iesgrancapitan-proyectos/202021asir_junio_ControlCalidadAire-escurtu696/Guiatecnica/1.PNG

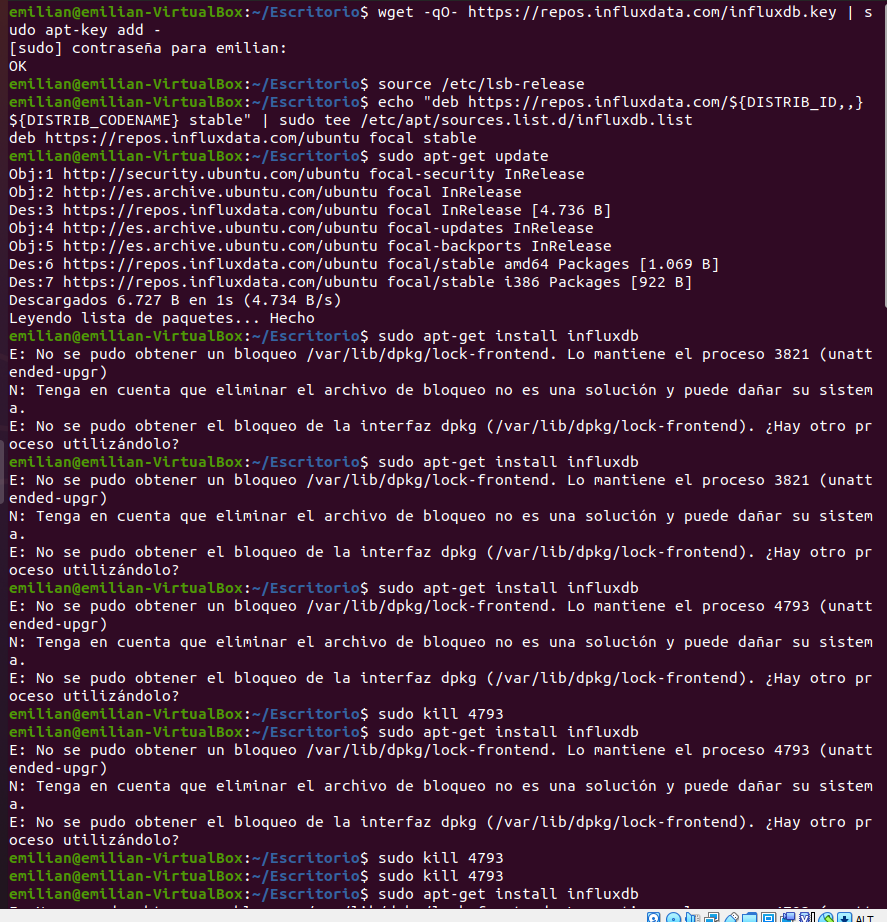
Guiatecnica/1.PNG
