iesgrancapitan-proyectos/202021asir_junio_ControlCalidadAire-escurtu696/Guiatecnica/2.PNG

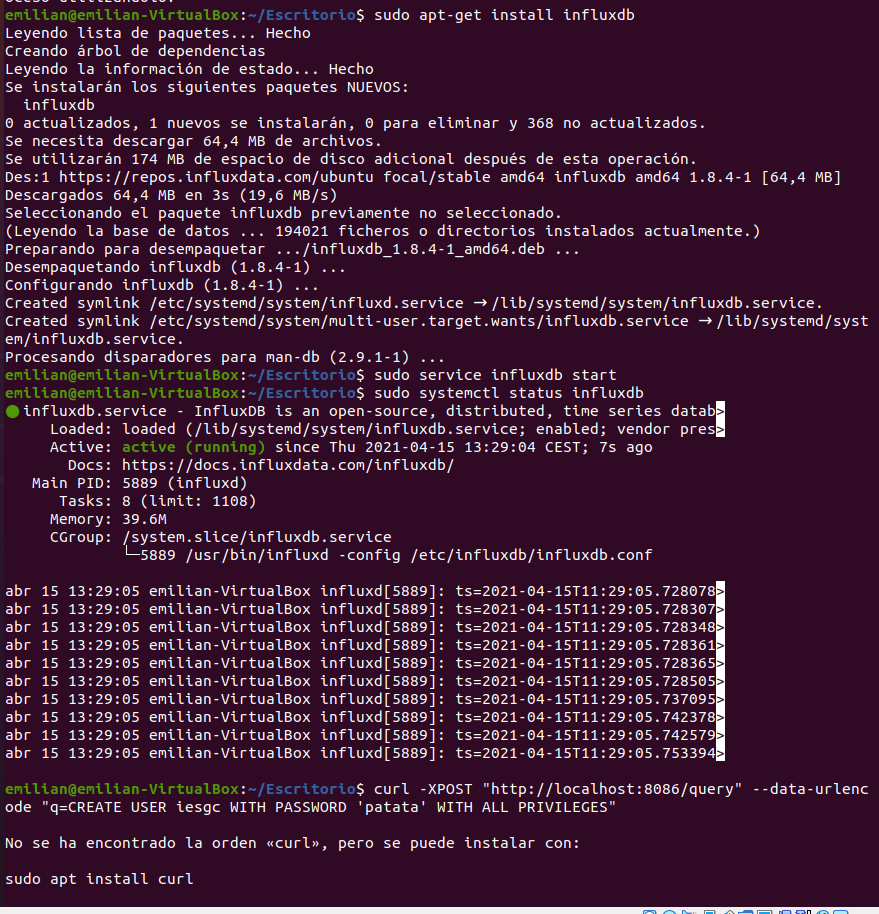
Guiatecnica/2.PNG
