iesgrancapitan-proyectos/202021asir_junio_ControlCalidadAire-escurtu696/Guiatecnica/3.PNG

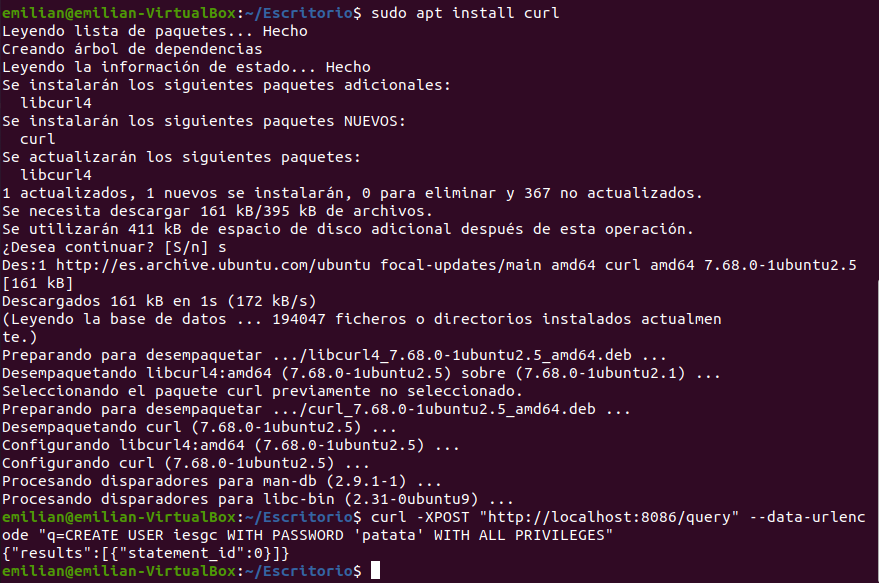
Guiatecnica/3.PNG
