iesgrancapitan-proyectos/202021asir_junio_ControlCalidadAire-escurtu696/Guiatecnica/4.PNG

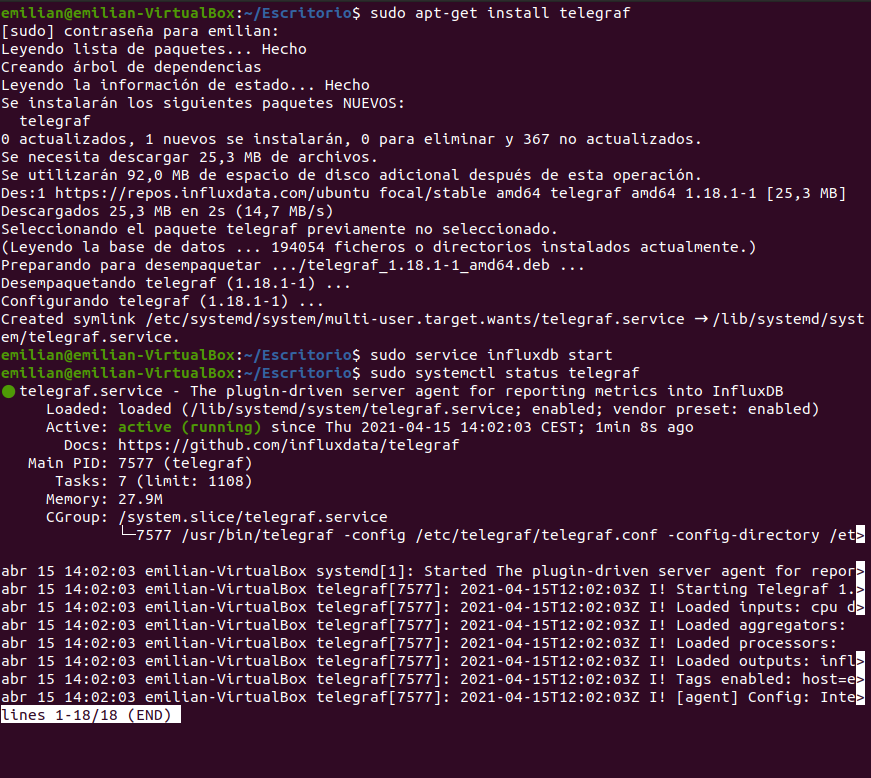
Guiatecnica/4.PNG
