iesgrancapitan-proyectos/202021asir_junio_ControlCalidadAire-escurtu696/Guiatecnica/5.PNG

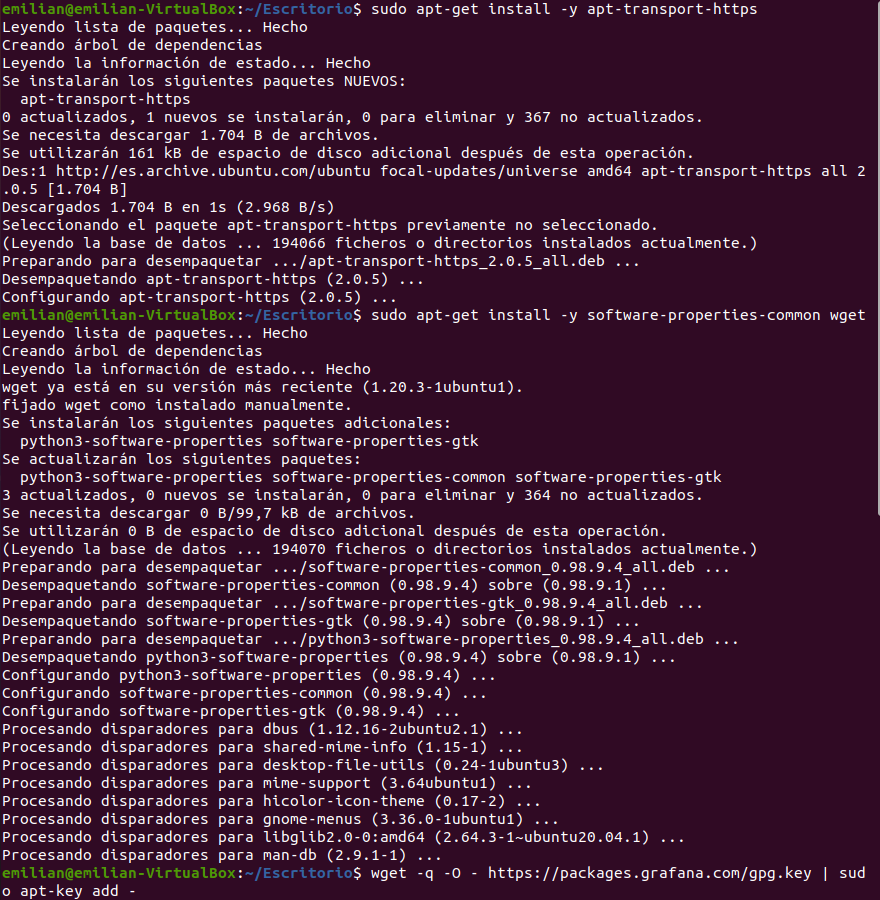
Guiatecnica/5.PNG
