iesgrancapitan-proyectos/202021asir_junio_ControlCalidadAire-escurtu696/Guiatecnica/6.PNG

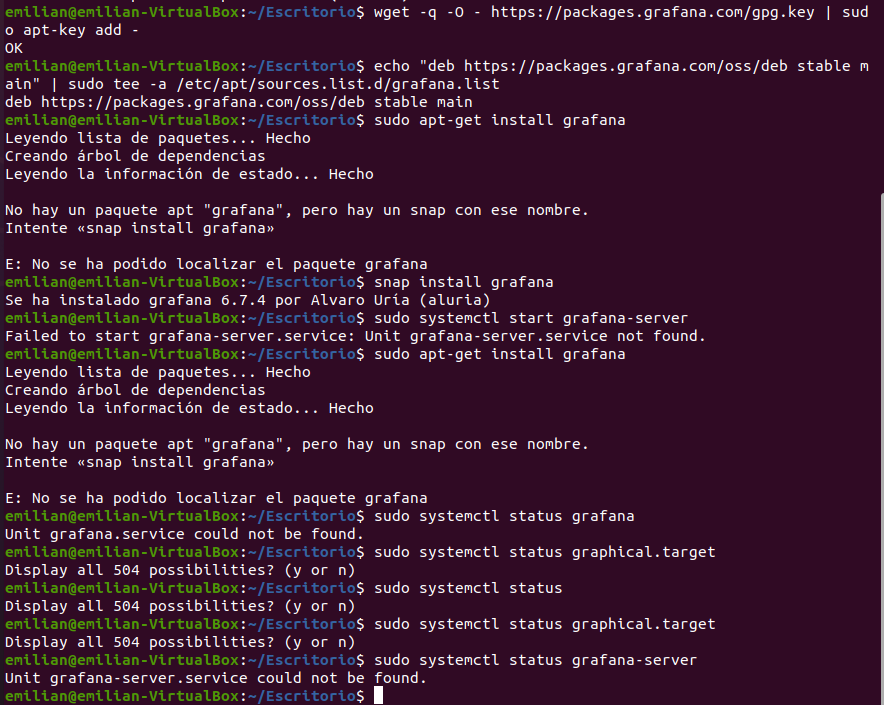
Guiatecnica/6.PNG
