iesgrancapitan-proyectos/202021asir_junio_ControlCalidadAire-escurtu696/Guiatecnica/7.PNG

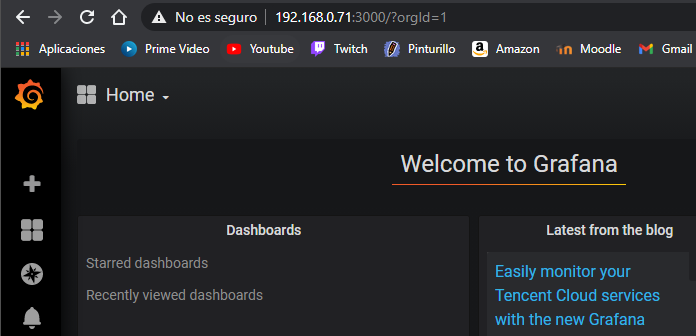
Guiatecnica/7.PNG
