iesgrancapitan-proyectos/202021asir_junio_ControlCalidadAire-escurtu696/Guiatecnica/8.PNG

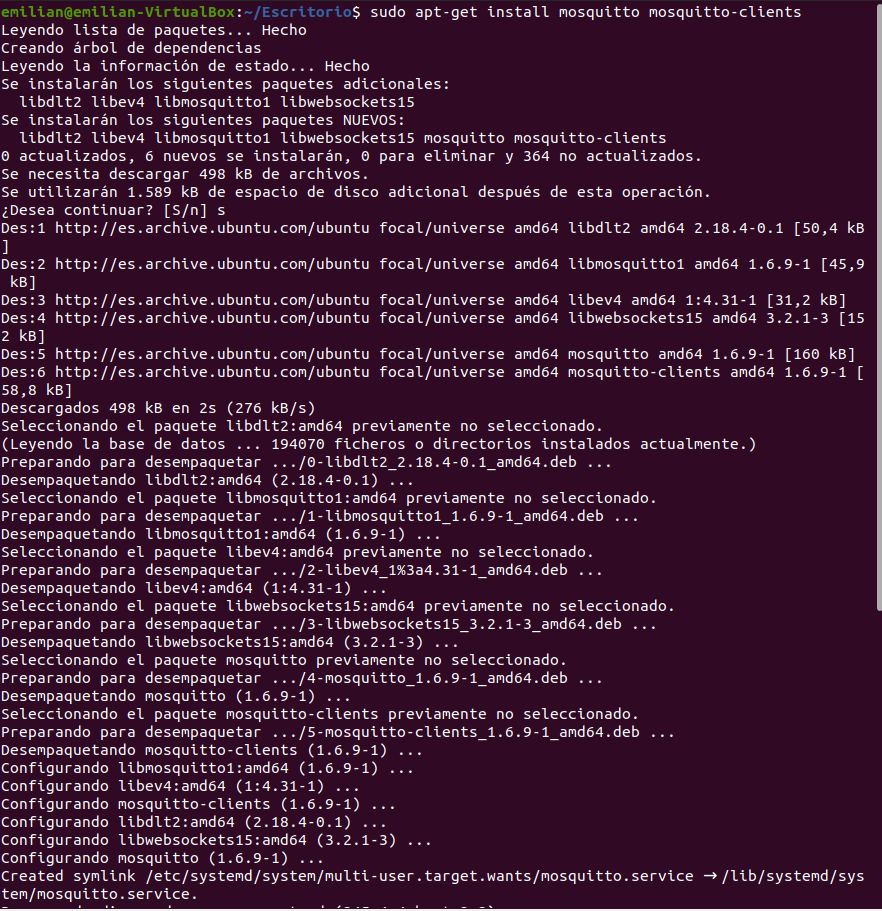
Guiatecnica/8.PNG
