iesgrancapitan-proyectos/202021asir_junio_ControlCalidadAire-escurtu696/Guiatecnica/9..PNG

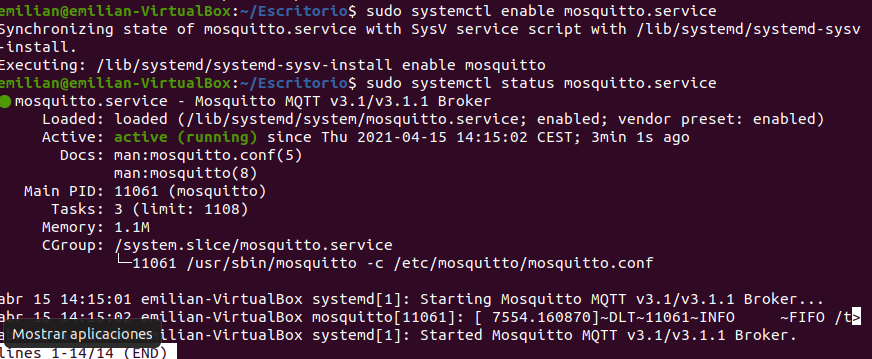
Guiatecnica/9..PNG
